phpbbireland/mioke80/blackpill_version/images/ayla80.png

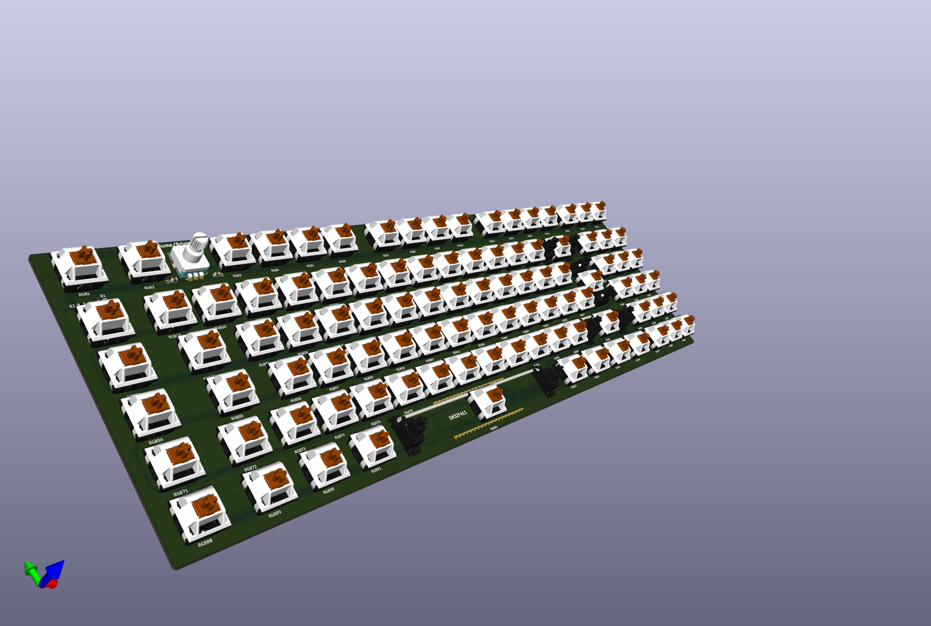
blackpill_version/images/ayla80.png
