phpbbireland/mioke80/blackpill_version/images/ayla80v2.png

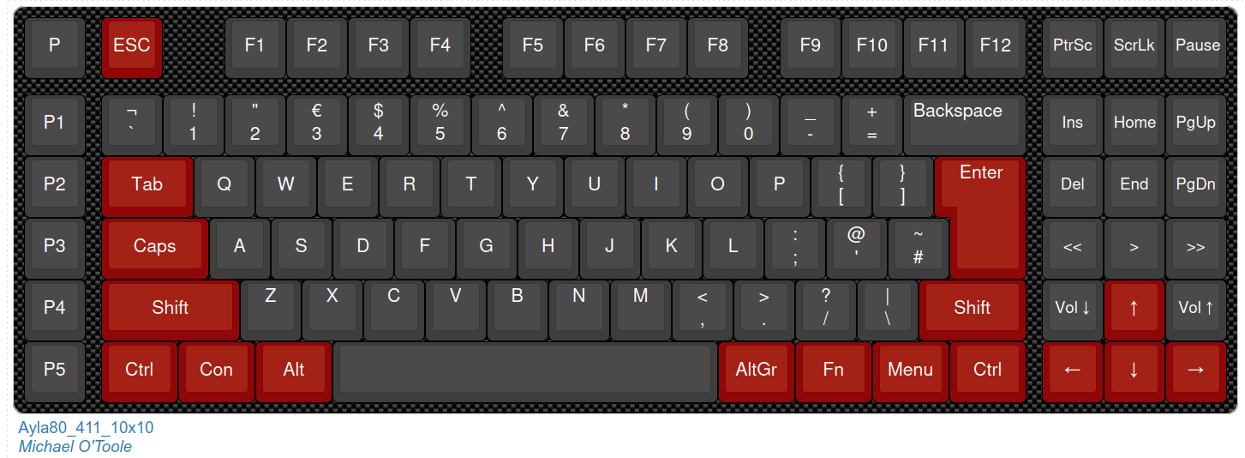
blackpill_version/images/ayla80v2.png
