phpbbireland/mioke80/blackpill_version/images/blackpill_board.png

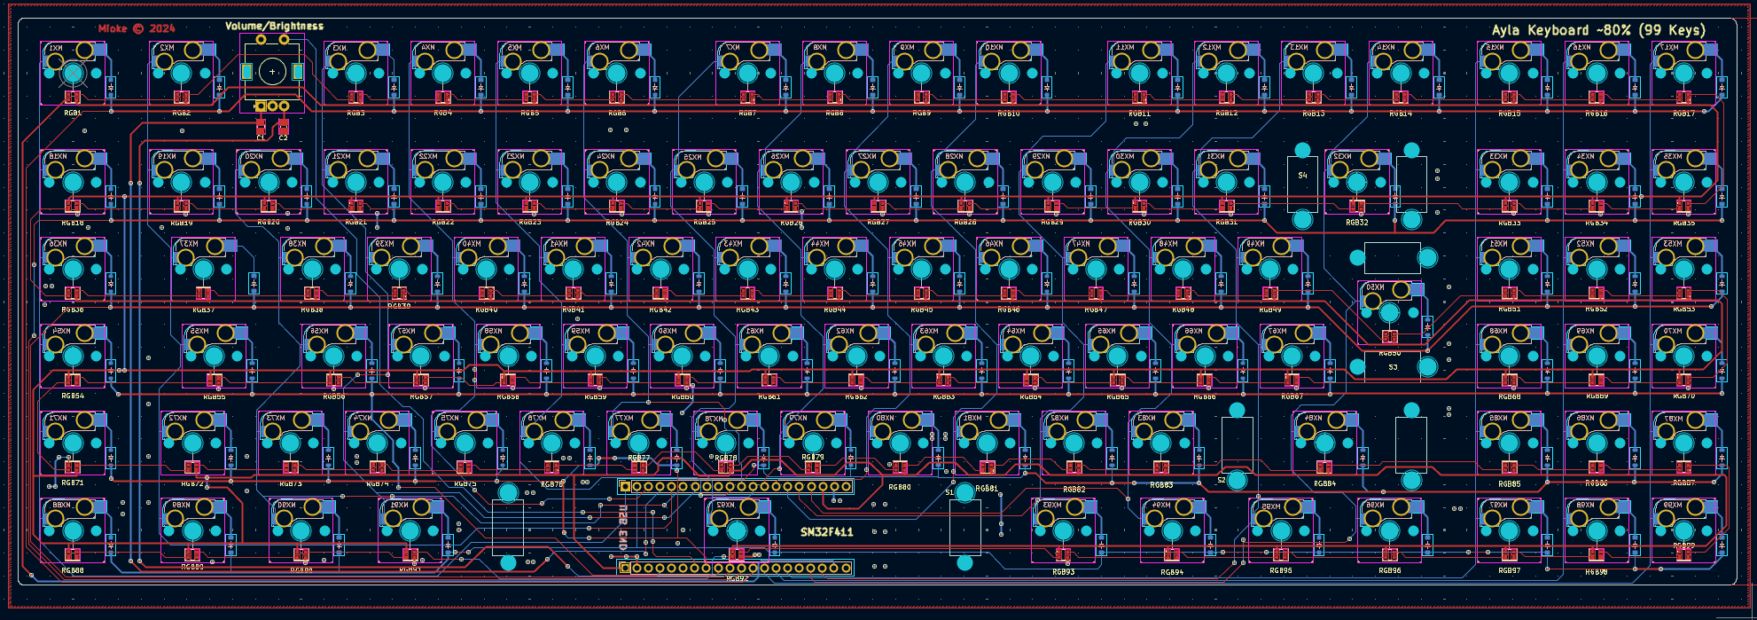
blackpill_version/images/blackpill_board.png
