phpbbireland/mioke80/blackpill_version/images/board_10x10_matrix_4Layer.png

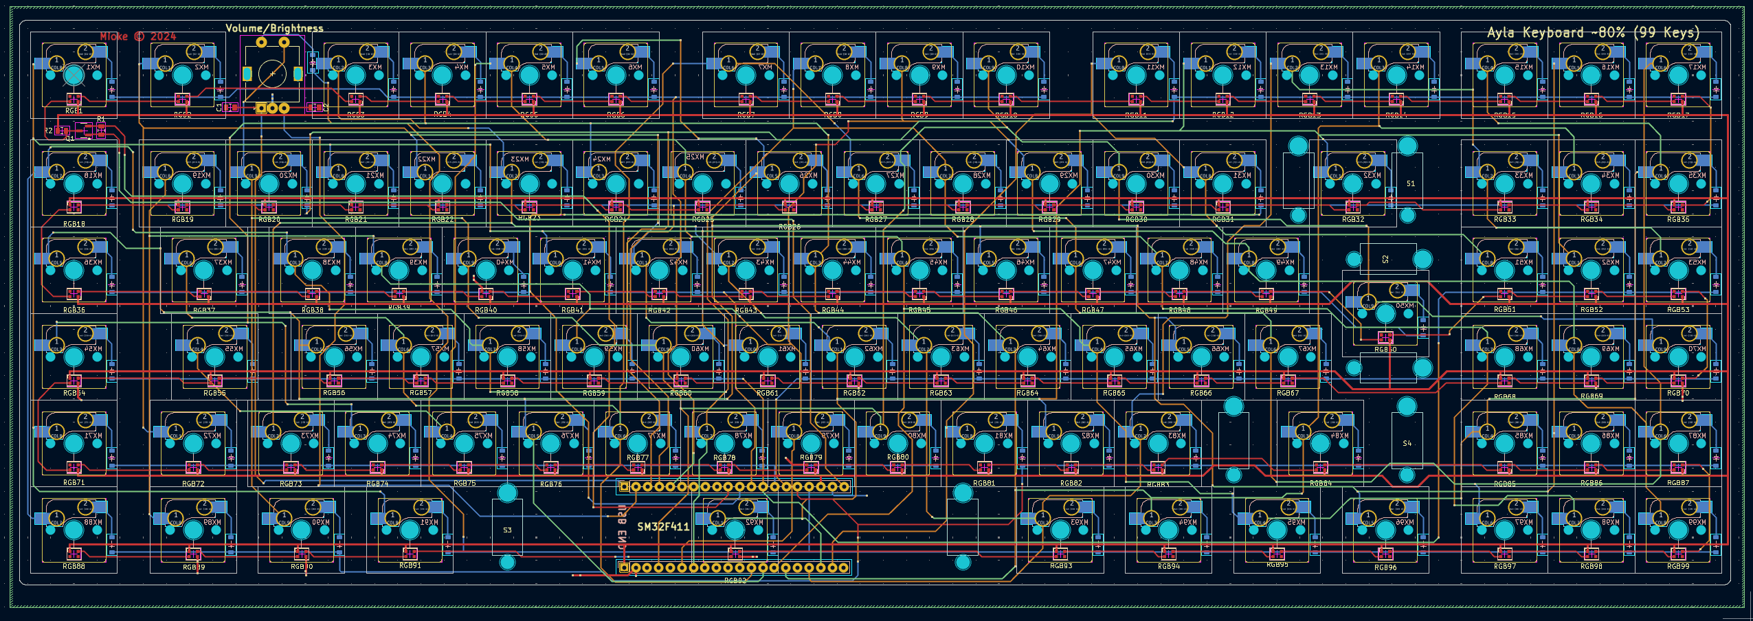
blackpill_version/images/board_10x10_matrix_4Layer.png
