phpbbireland/mioke80/blackpill_version/images/keyboard_layout_iso.PNG

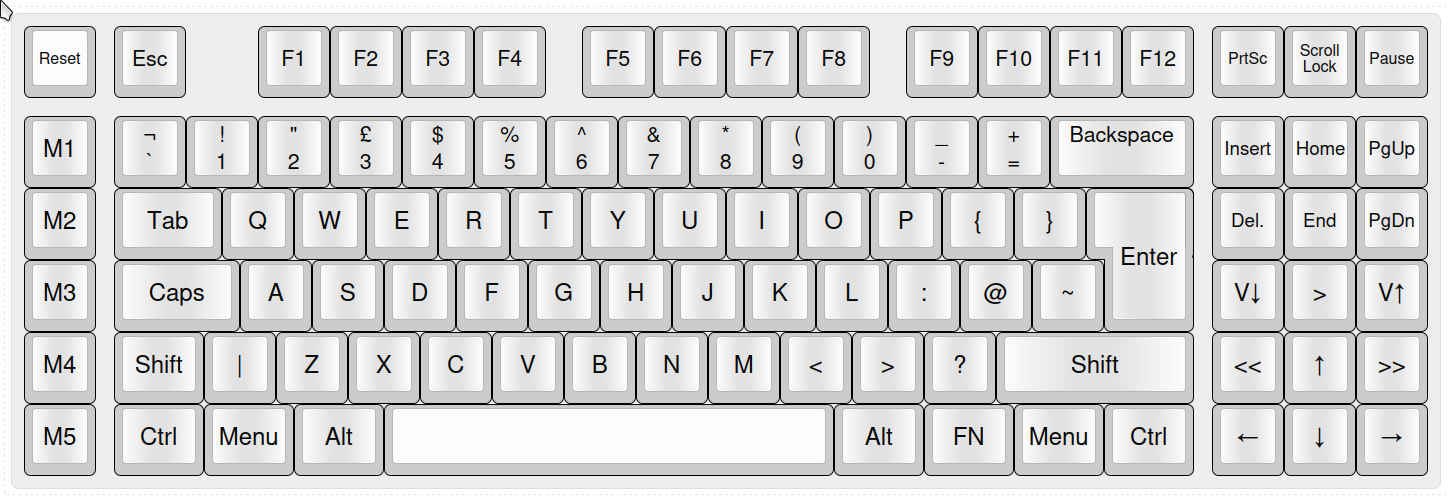
blackpill_version/images/keyboard_layout_iso.PNG
