phpbbireland/mioke80/blackpill_version/images/sch_matrix.png

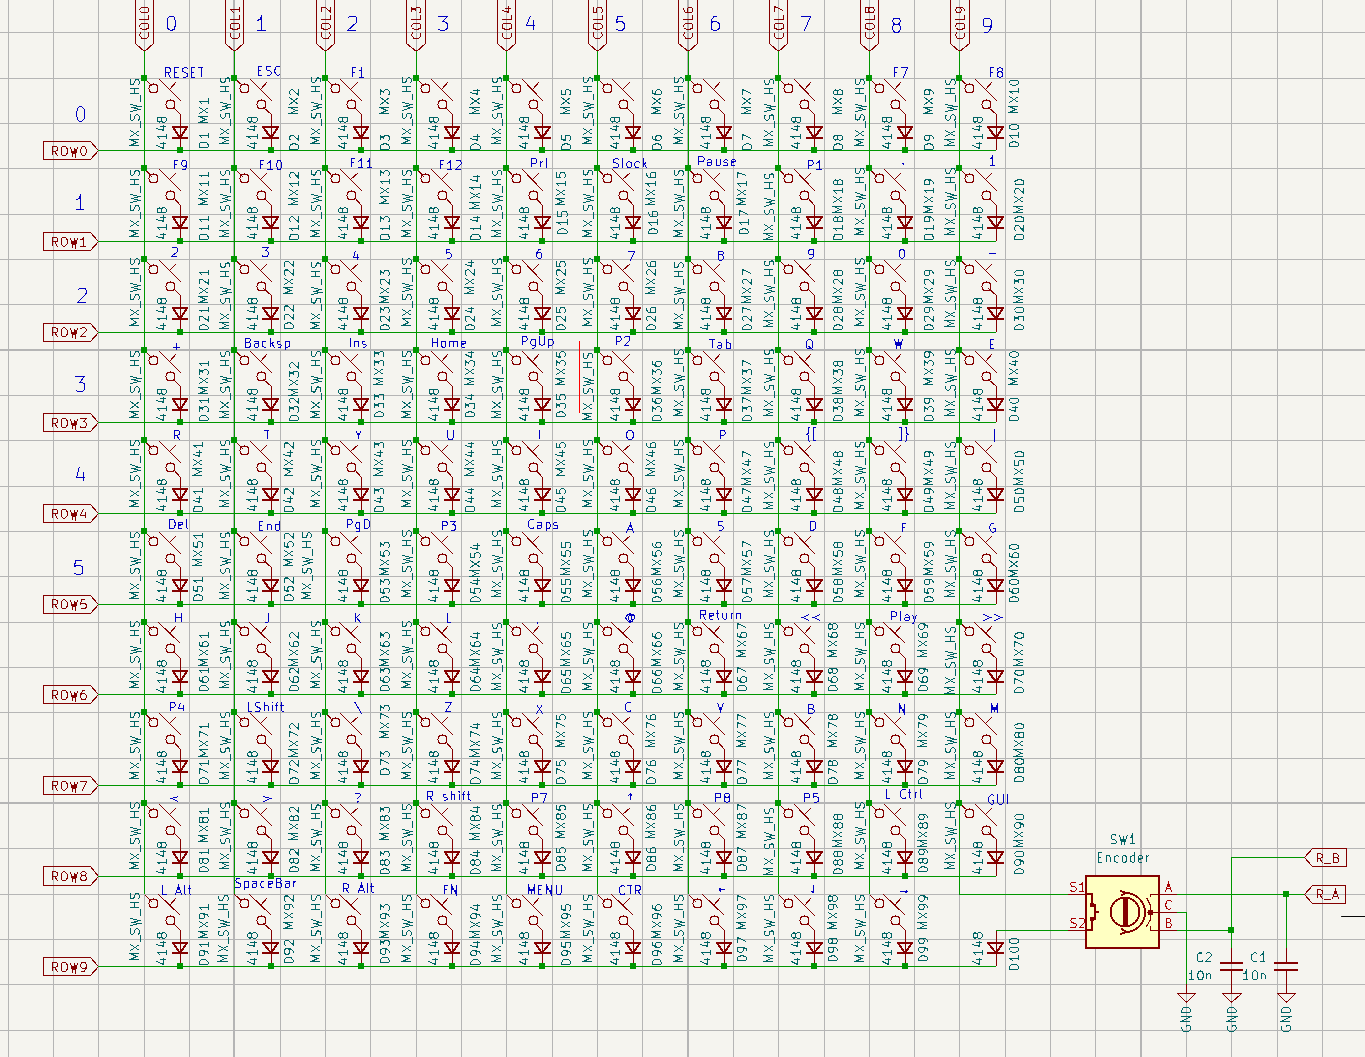
blackpill_version/images/sch_matrix.png
