phpbbireland/mioke80/images/keyboard-layout.png

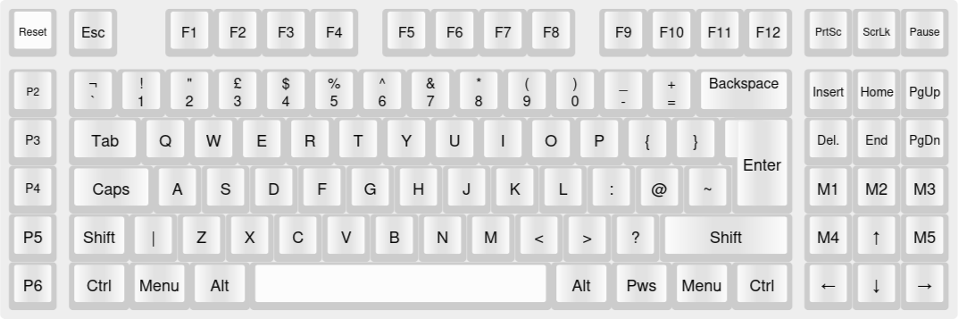
images/keyboard-layout.png
