phpbbireland/mioke80/images/keyboard_layout_iso_fancy.png

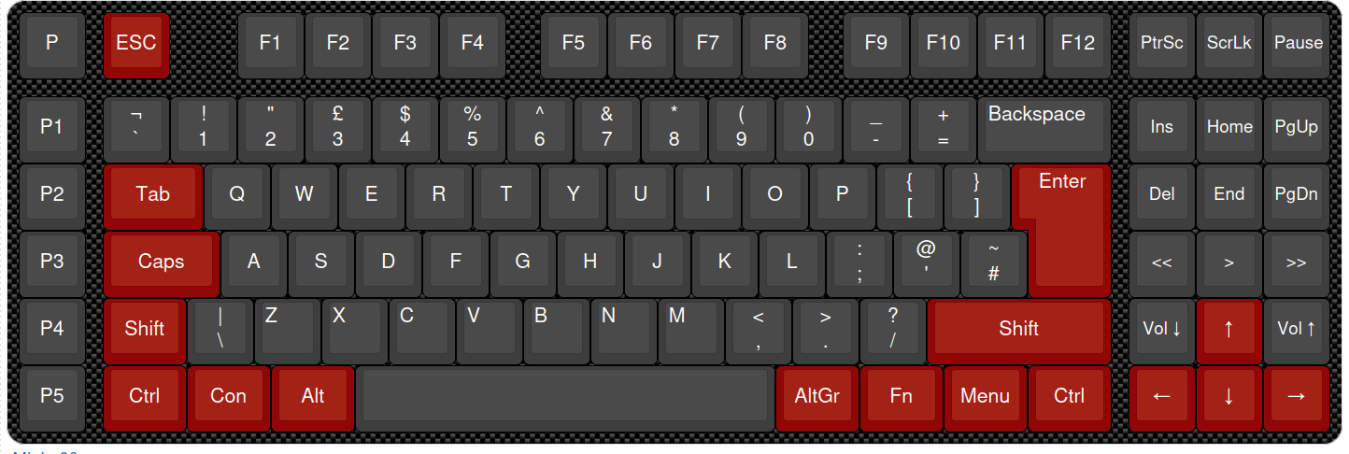
images/keyboard_layout_iso_fancy.png
