phpbbireland/mioke80/images/Mioke80.jpg

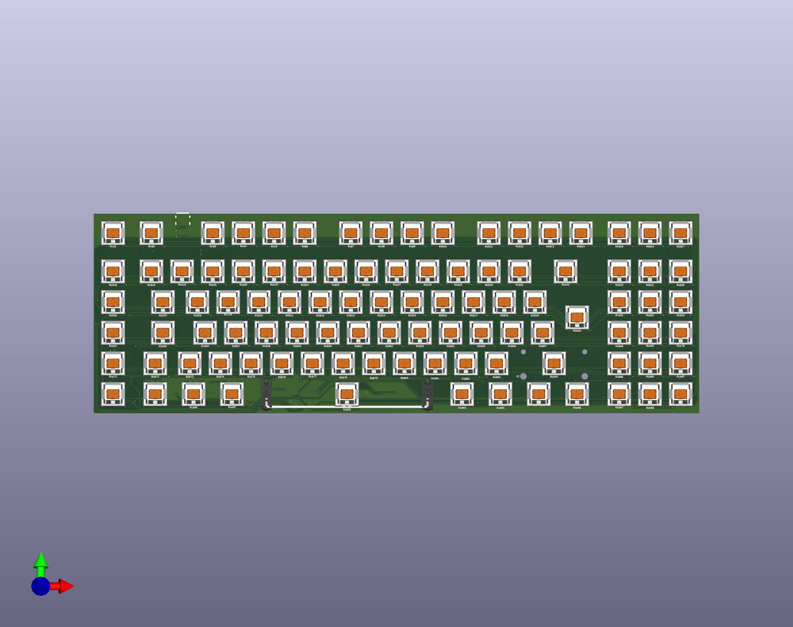
images/Mioke80.jpg
