phpbbireland/mioke80/images/Mioke80_back.jpg

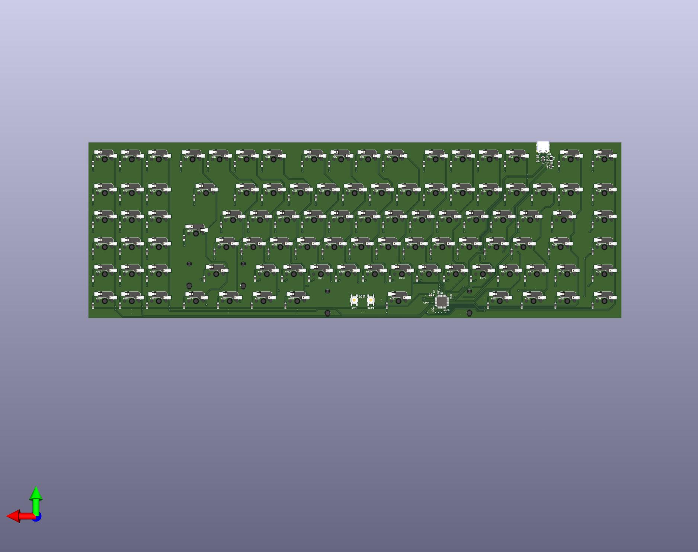
images/Mioke80_back.jpg
