phpbbireland/mioke80/images/MX_SW_HS.png

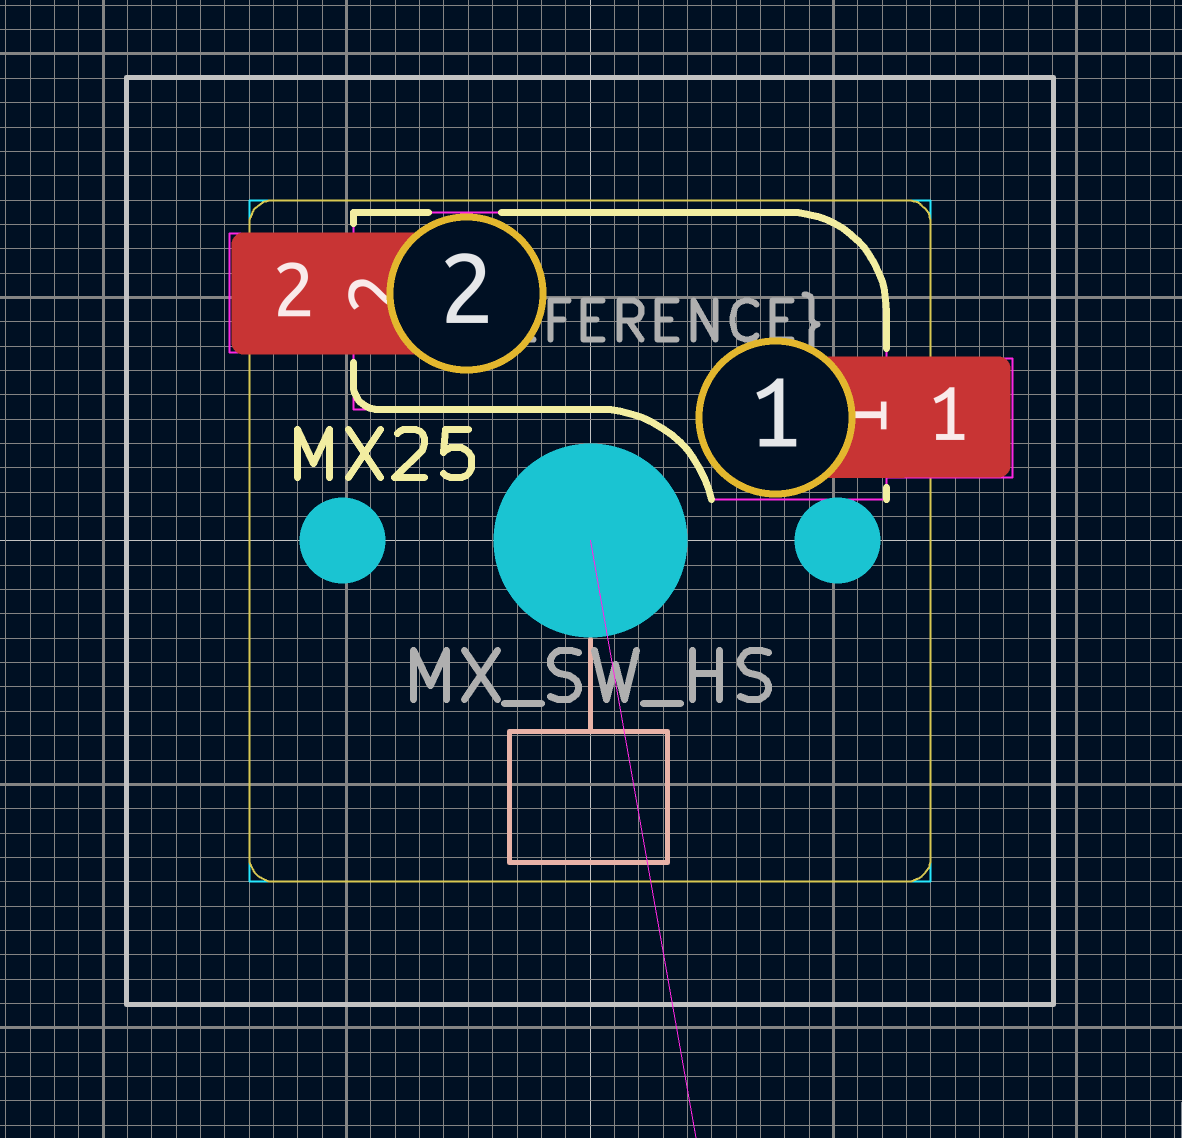
images/MX_SW_HS.png
