phpbbireland/mioke80/images/schematic_image_micro.png

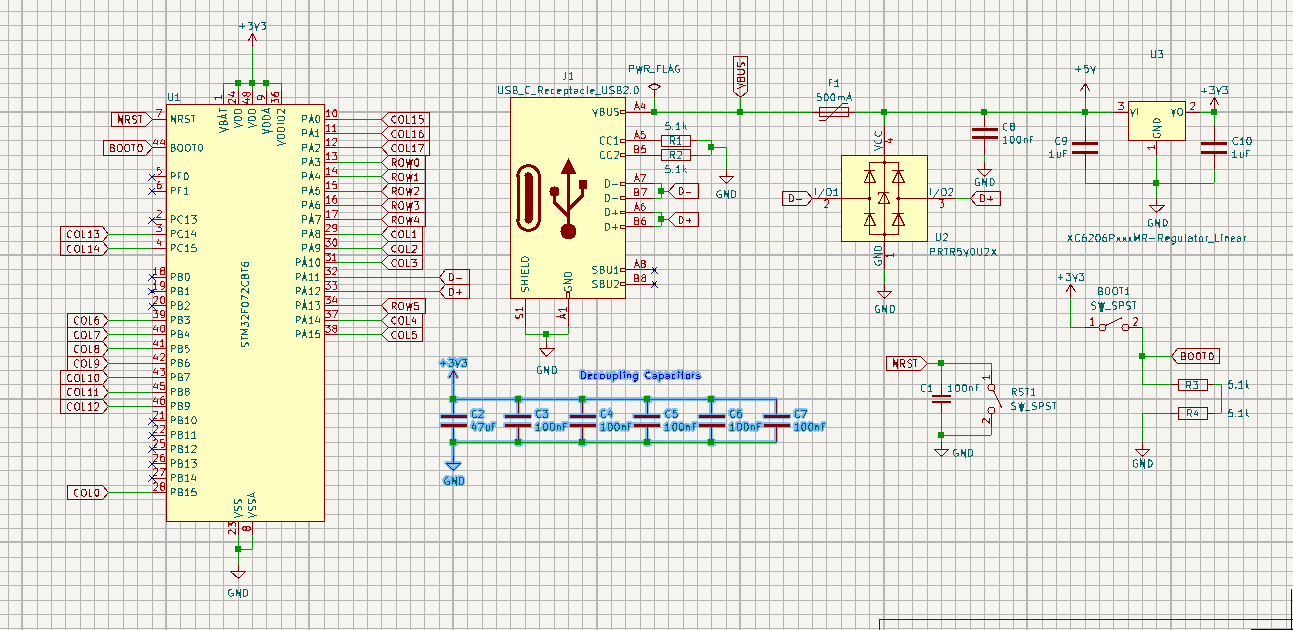
images/schematic_image_micro.png
