phpbbireland/mioke80/images/switch summary.png

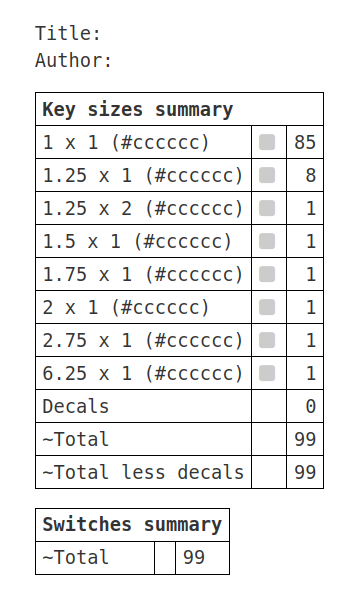
images/switch summary.png
