phpbbireland/mioke80/blackpill_version/QMK/ayla_411/halconf.h

#pragma once

#define HAL_USE_I2C FALSE
#define HAL_USE_SERIAL TRUE
#define HAL_USE_PWM TRUE
#define HAL_USE_SPI TRUE
#define SPI_USE_WAIT TRUE
#define SPI_SELECT_MODE SPI_SELECT_MODE_PAD

#include_next <halconf.h>
